ryood/3340VCO/3340VCO性能測定/3340VCO_1kHz.png

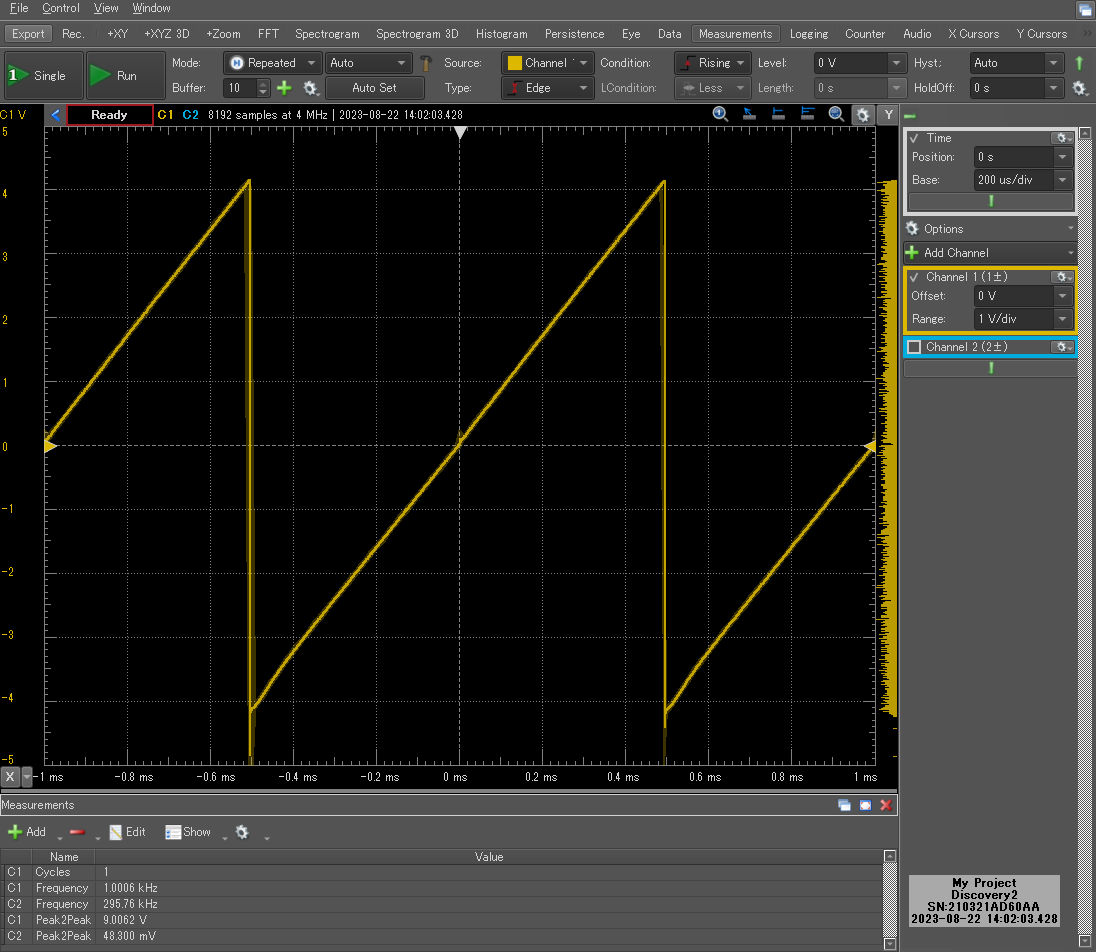
3340VCO性能測定/3340VCO_1kHz.png
