ryood/3340VCO/3340VCO性能測定/3340VCO_CV_Frequency.png

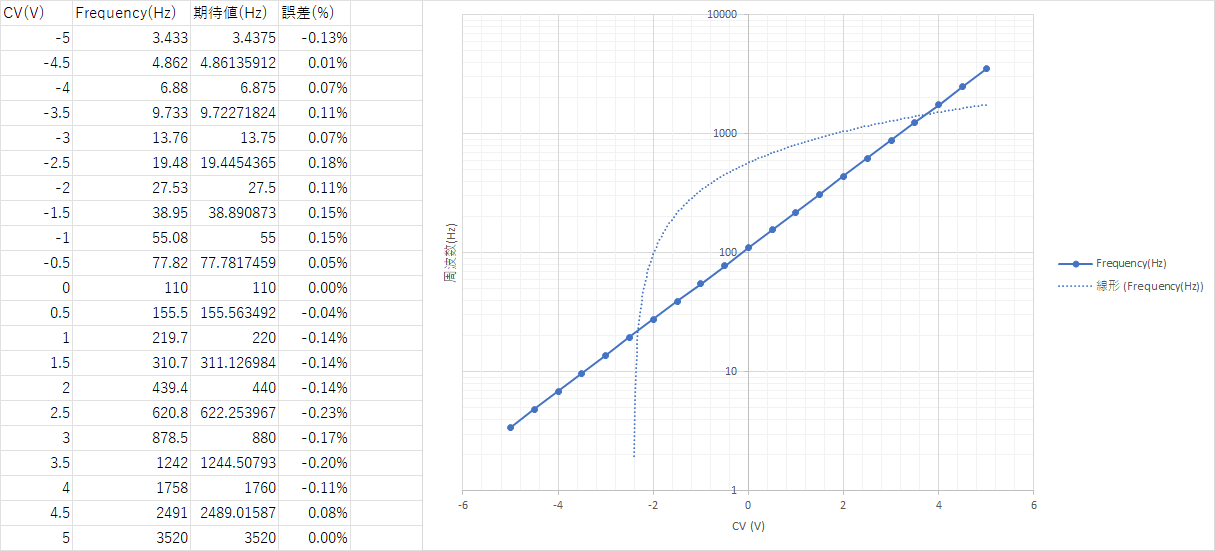
3340VCO性能測定/3340VCO_CV_Frequency.png
