ryood/3340VCO/3340VCO性能測定/3340VCO_SAW_3.43Hz.png

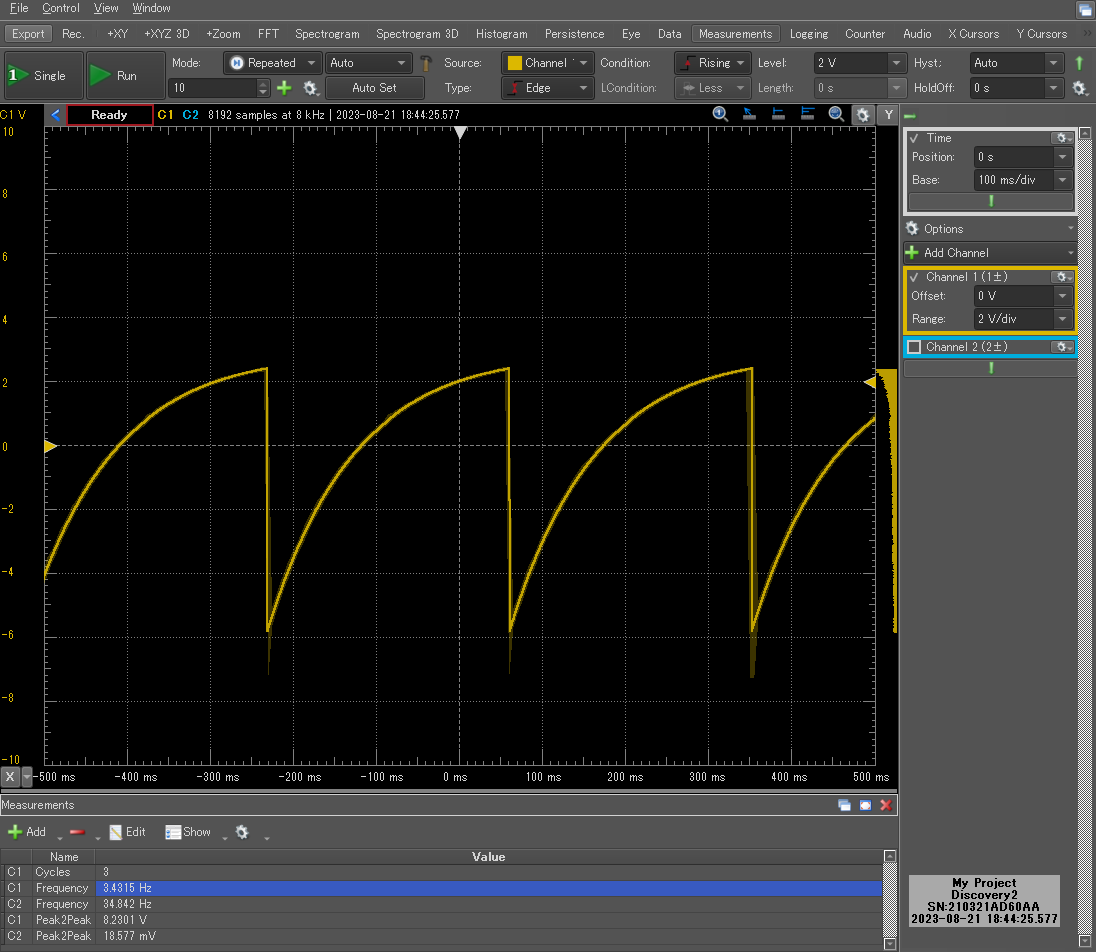
3340VCO性能測定/3340VCO_SAW_3.43Hz.png
