ryood/3340VCO/3340VCO性能測定/3340VCO_Ver.1.1_sch.png

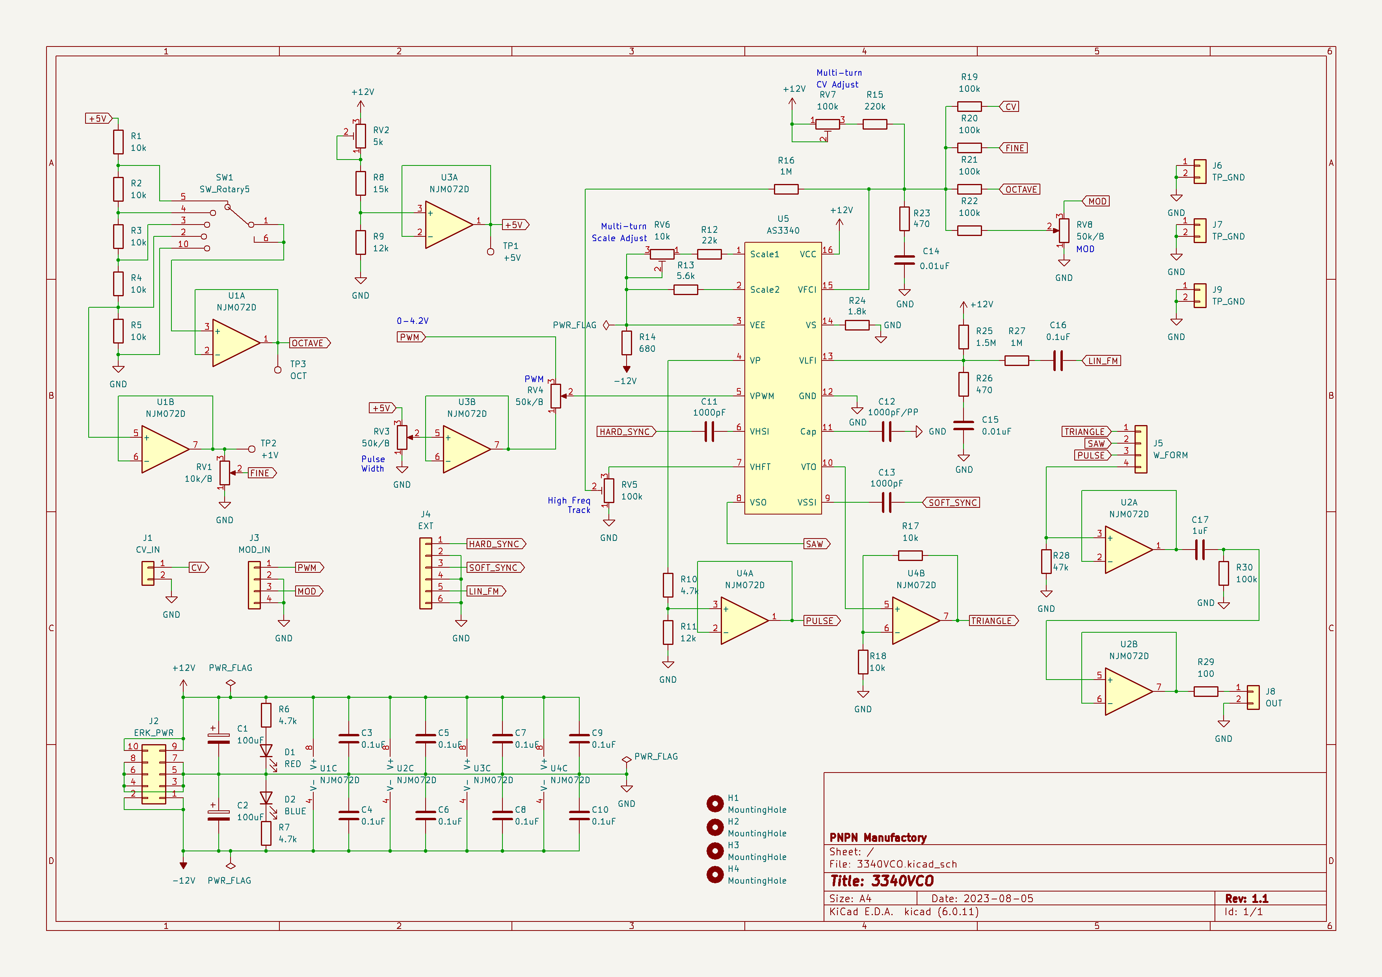
3340VCO性能測定/3340VCO_Ver.1.1_sch.png
