ryood/3340VCO/3340VCO性能測定/AC_CPL_NO.png

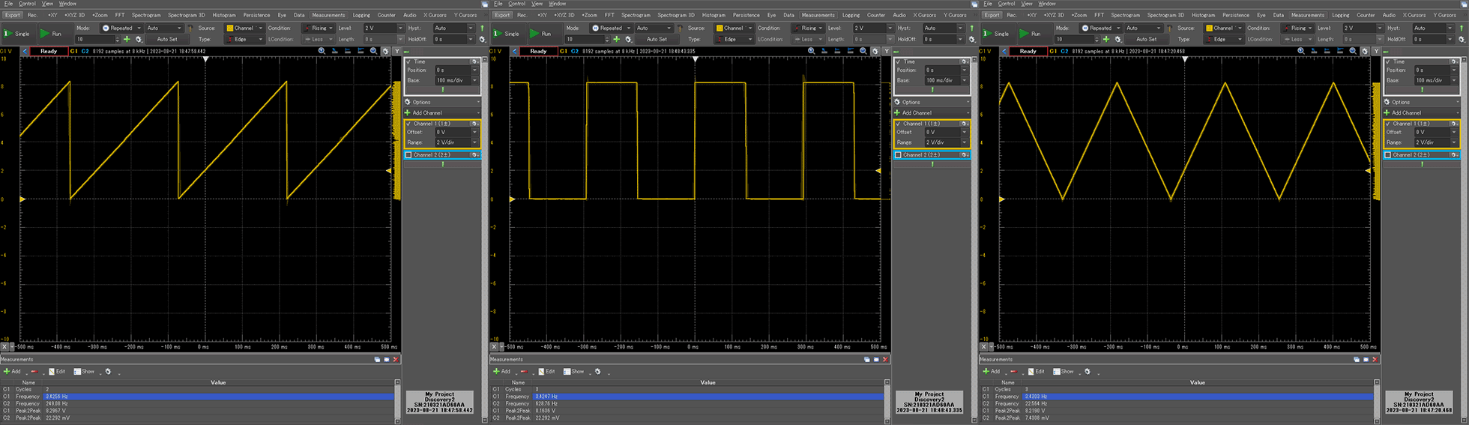
3340VCO性能測定/AC_CPL_NO.png
