ryood/3340VCO/3340VCO性能測定/adder_sim.png

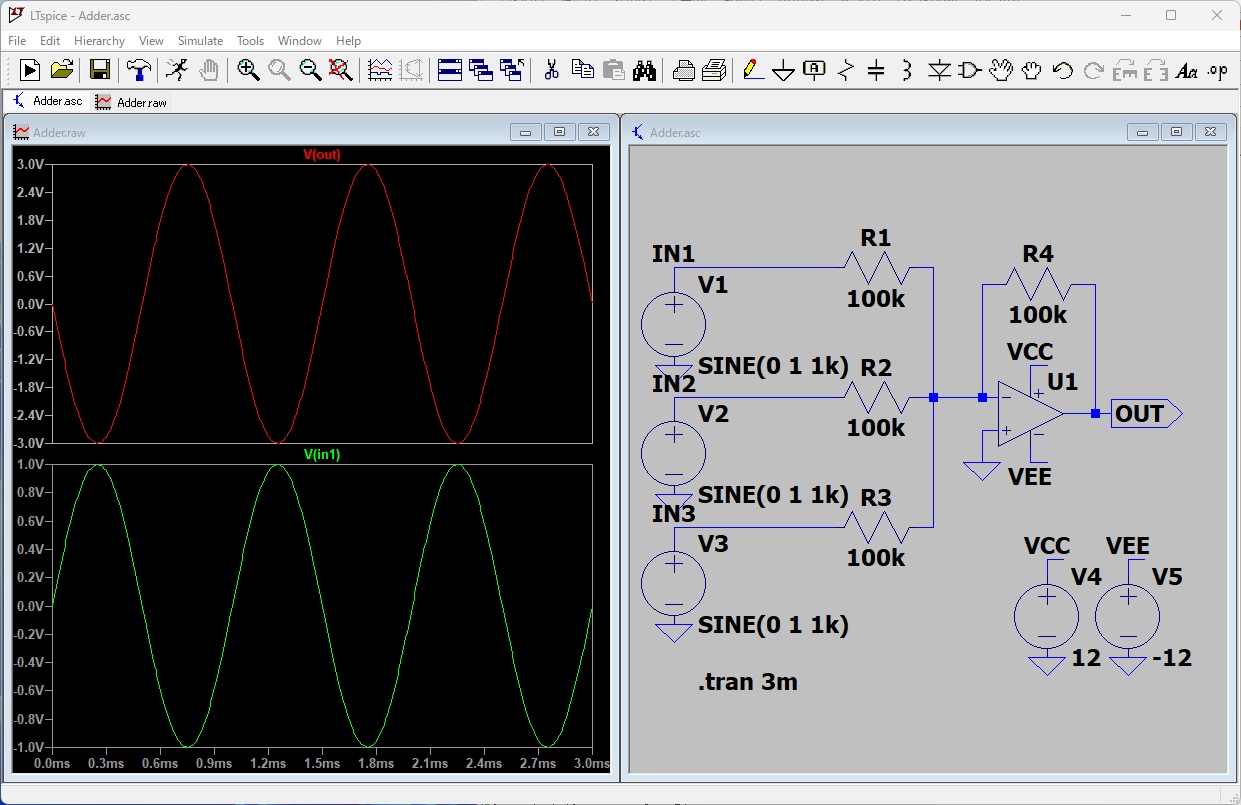
3340VCO性能測定/adder_sim.png
