ryood/3340VCO/3340VCO性能測定/AS3340.png

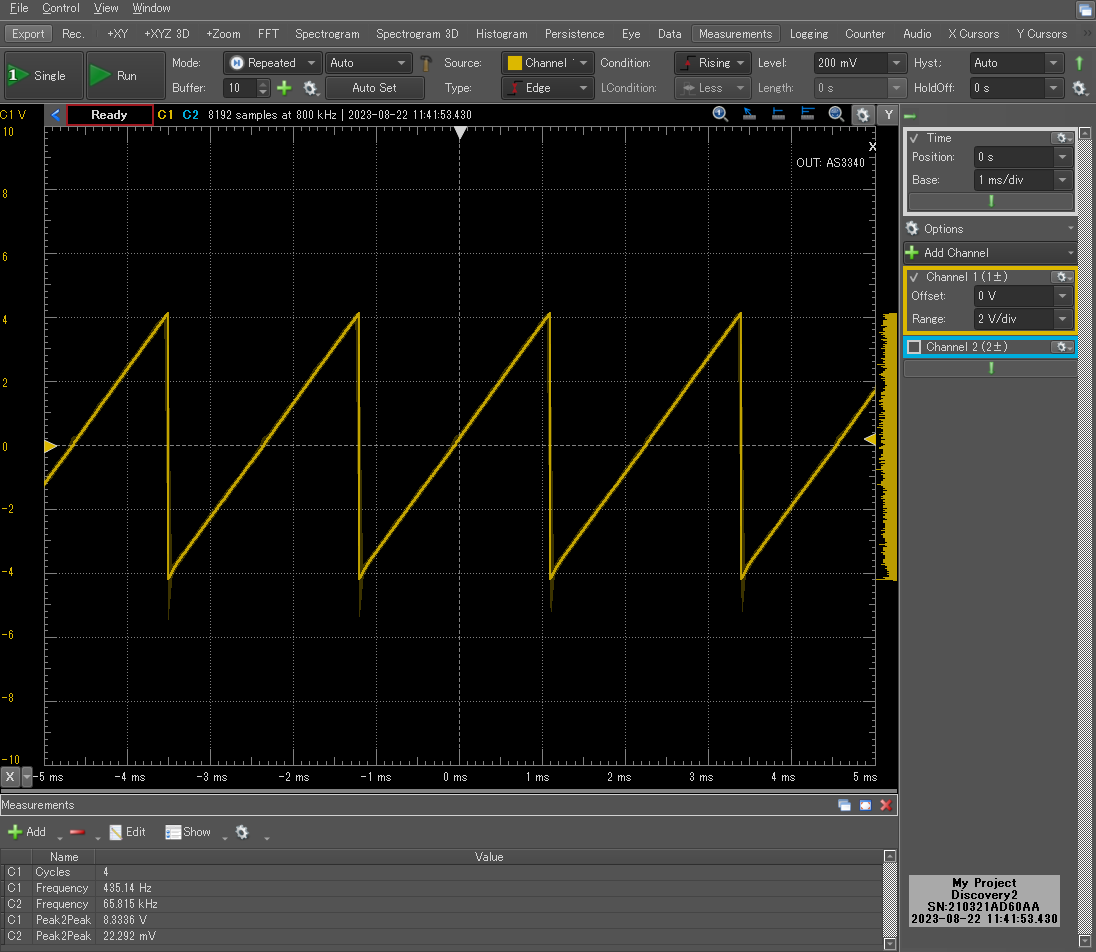
3340VCO性能測定/AS3340.png
