ryood/3340VCO/3340VCO性能測定/HardSync.png

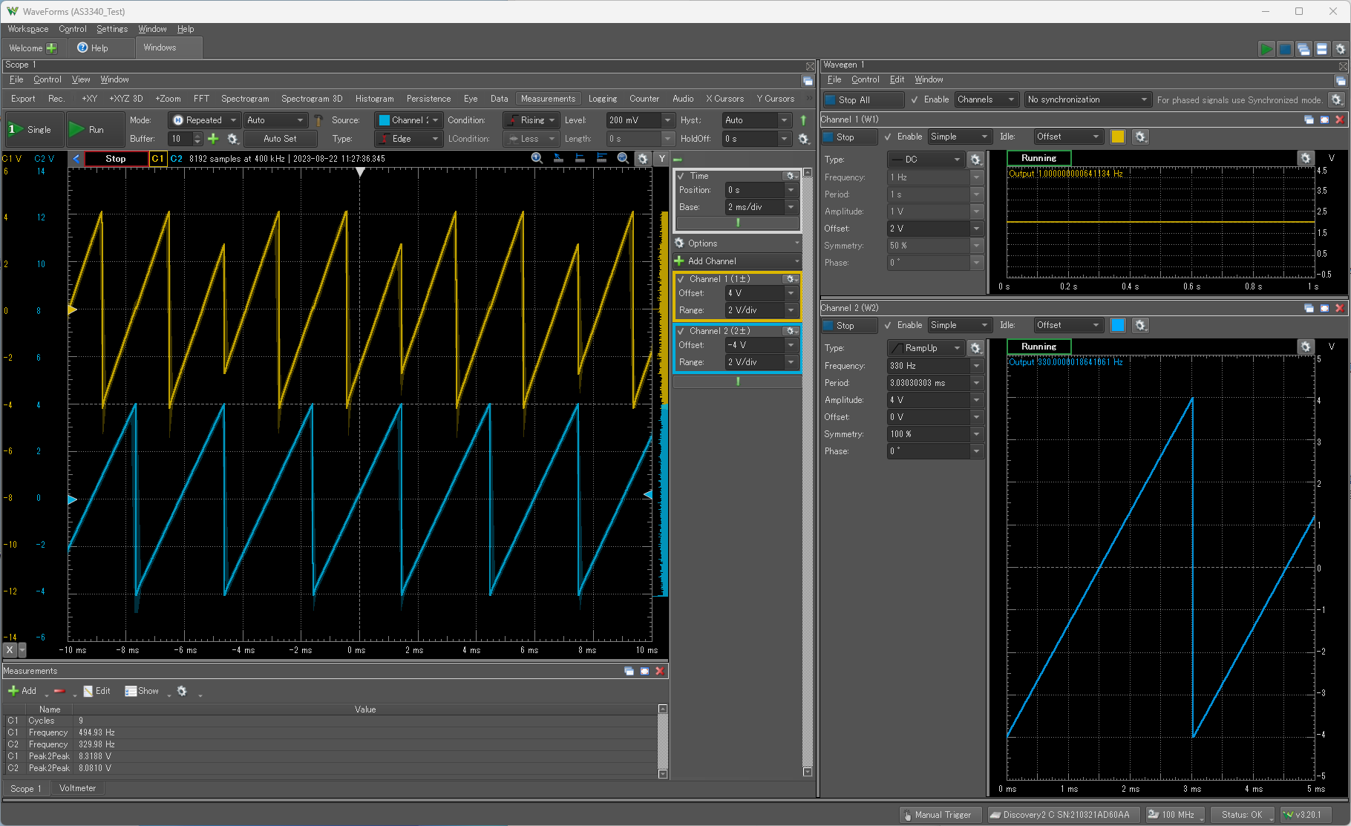
3340VCO性能測定/HardSync.png
