ryood/3340VCO/3340VCO性能測定/LinFM.png

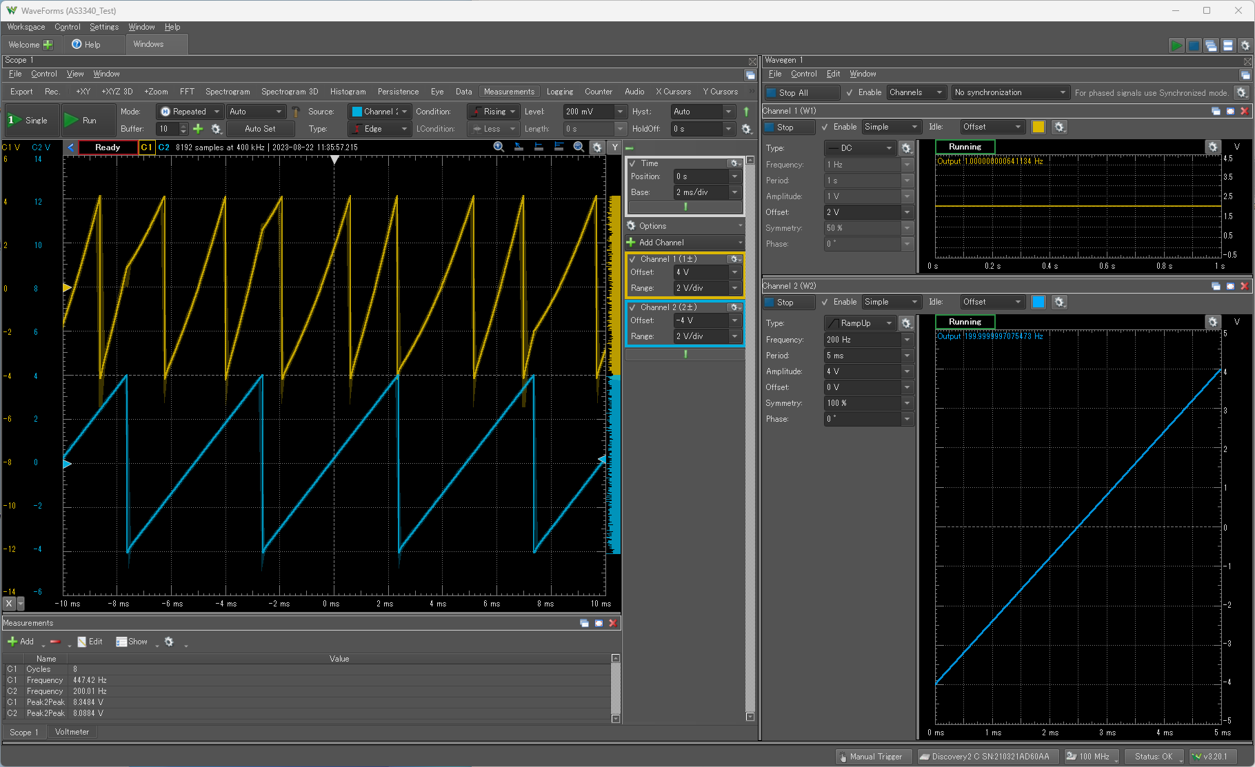
3340VCO性能測定/LinFM.png
