ryood/3340VCO/3340VCO性能測定/MOD_FM.png

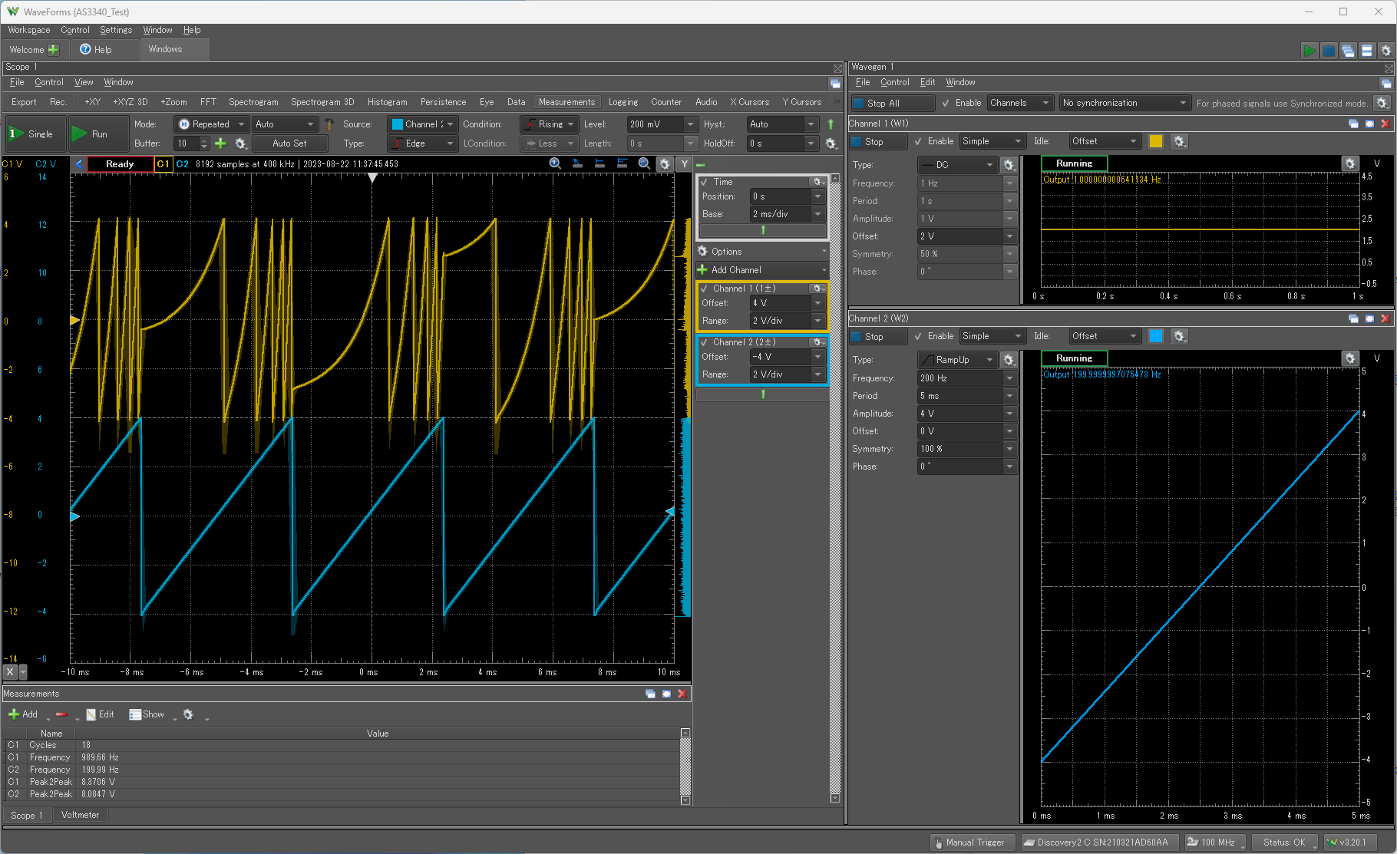
3340VCO性能測定/MOD_FM.png
