ryood/3340VCO/3340VCO性能測定/NO_AC_CPL_3340VCO_SQR_3.43Hz.png

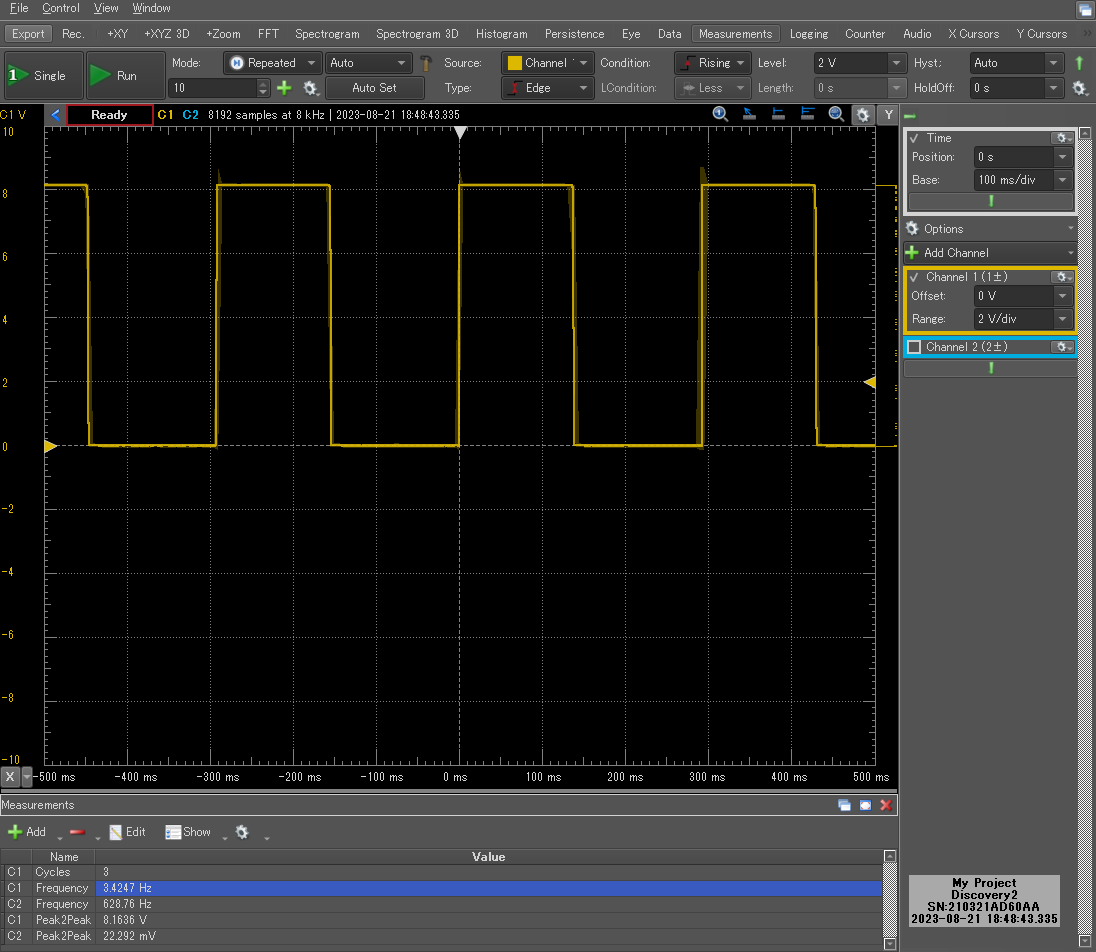
3340VCO性能測定/NO_AC_CPL_3340VCO_SQR_3.43Hz.png
