ryood/3340VCO/3340VCO性能測定/PCM2704_1kHz.png

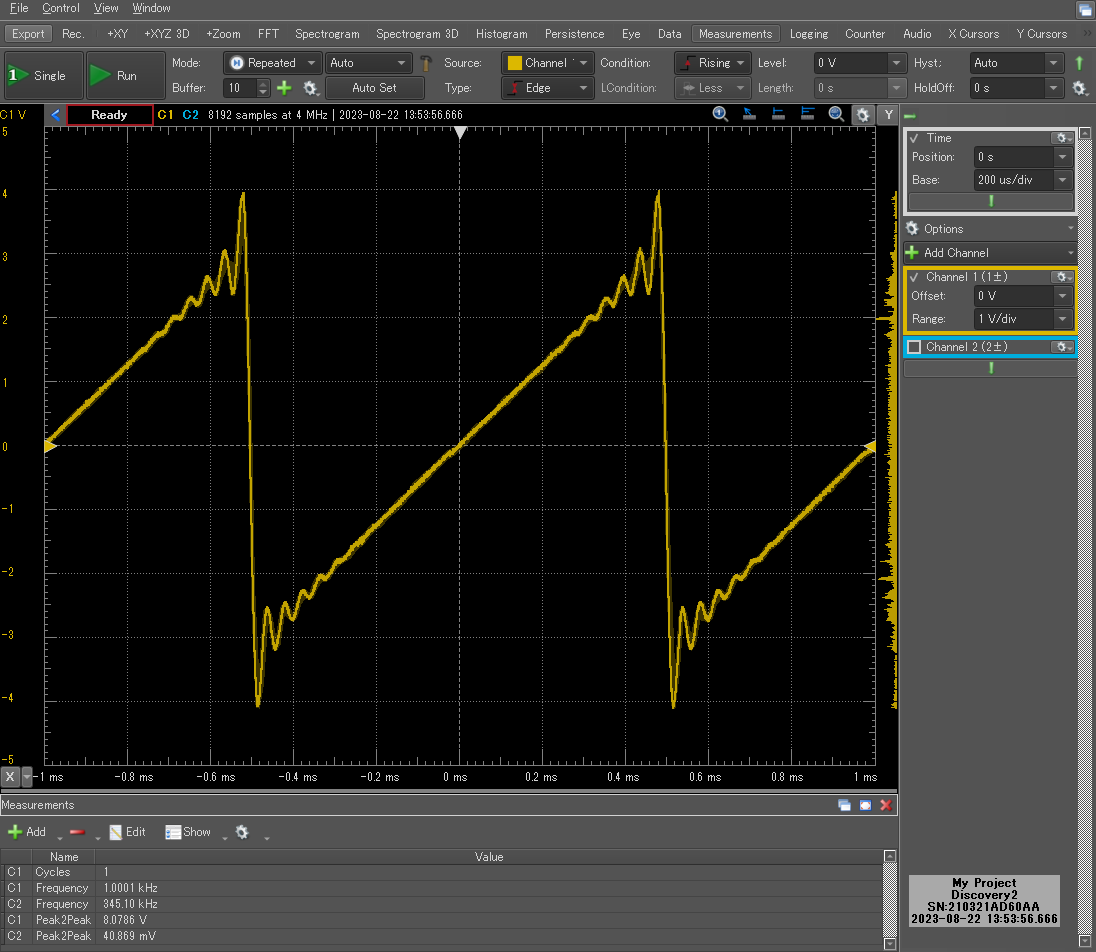
3340VCO性能測定/PCM2704_1kHz.png
