ryood/3340VCO/3340VCO性能測定/SardSync.png

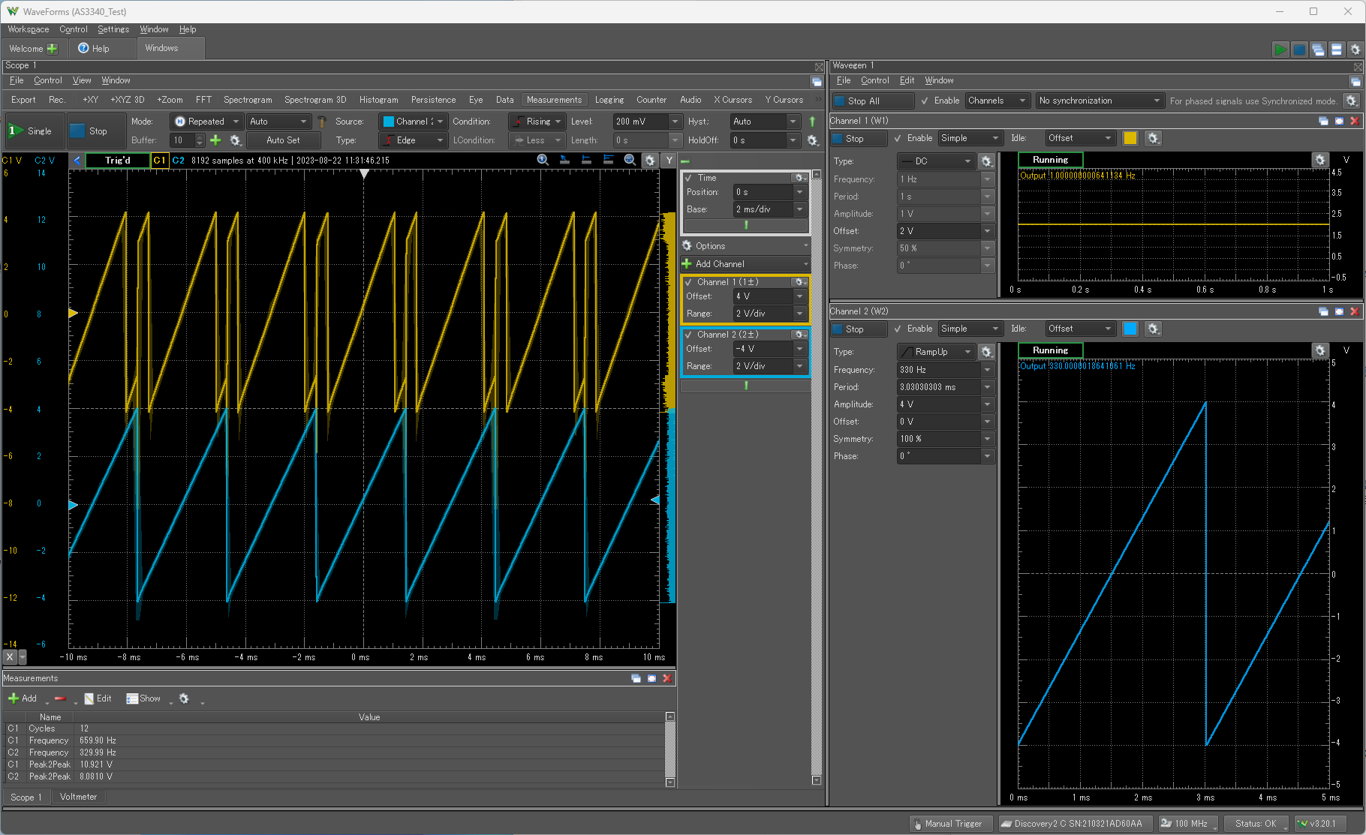
3340VCO性能測定/SardSync.png
