ryood/3340VCO/CAD/3340VCO_panel_tn.png

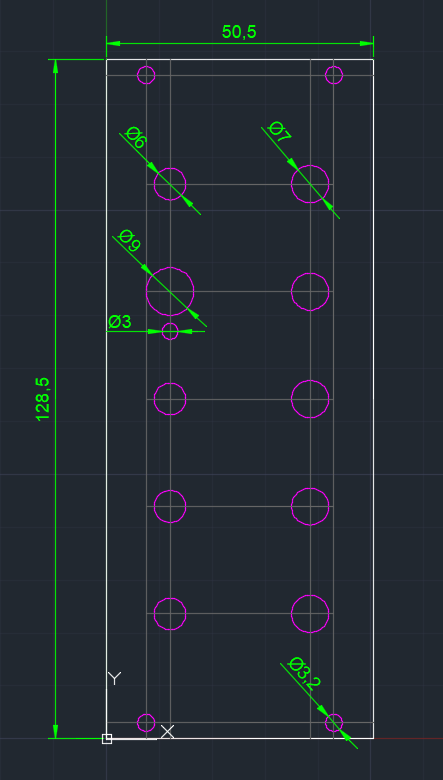
CAD/3340VCO_panel_tn.png
