ryood/3340VCO/etc/Nat_Tsuraichi.jpg

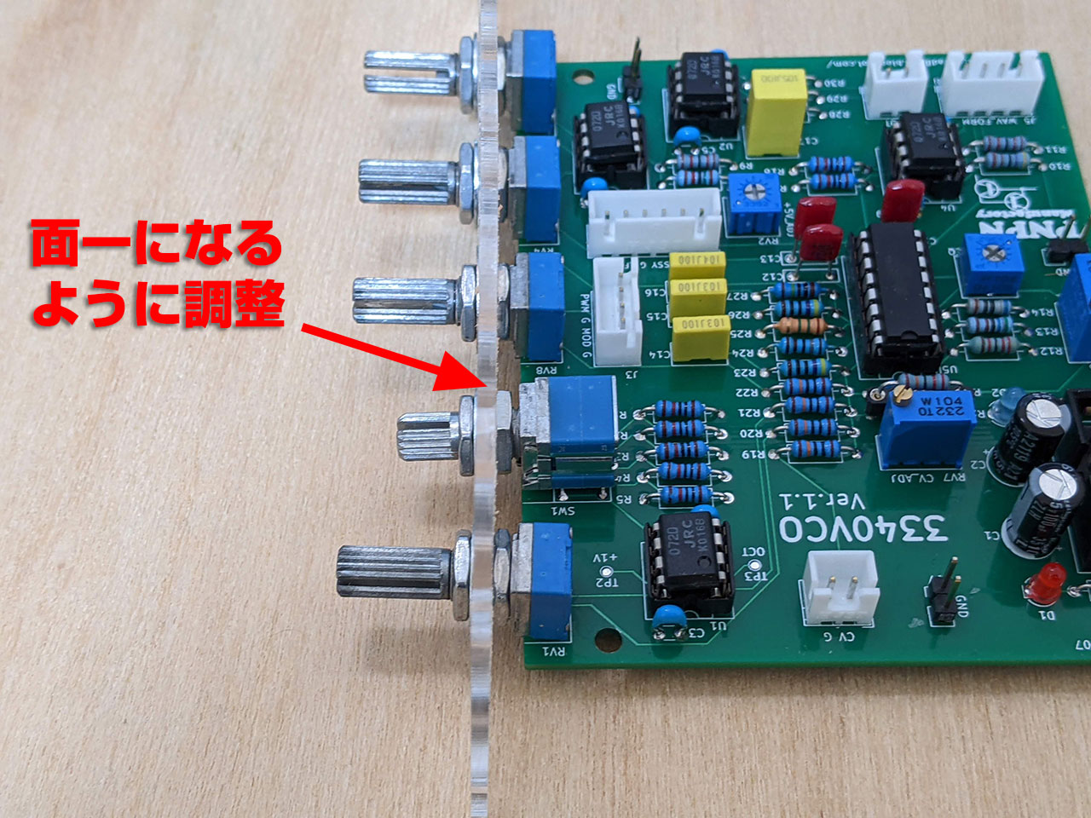
etc/Nat_Tsuraichi.jpg
