ryood/3340VCO/etc/Panel_Nat.jpg

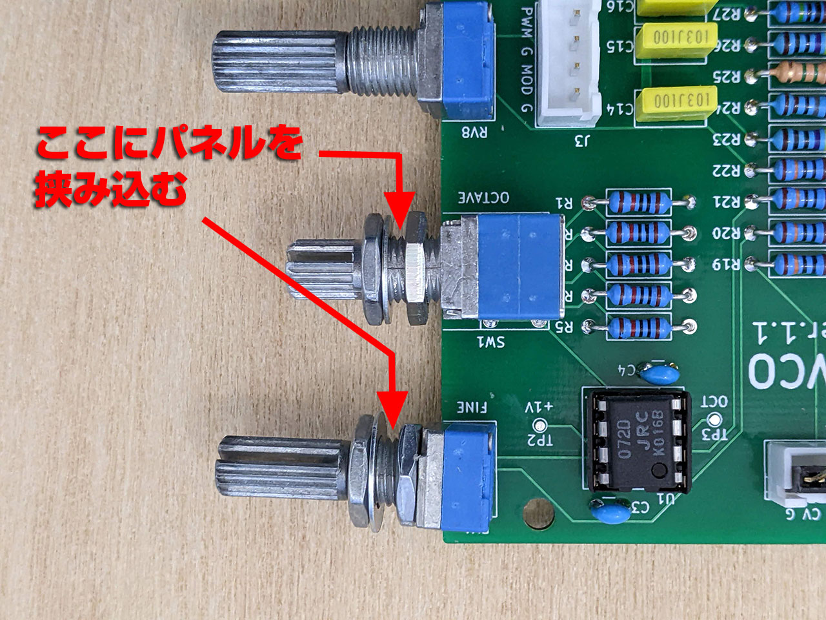
etc/Panel_Nat.jpg
