ryood/3340VCO/etc/PXL_20230715_094157501.jpg

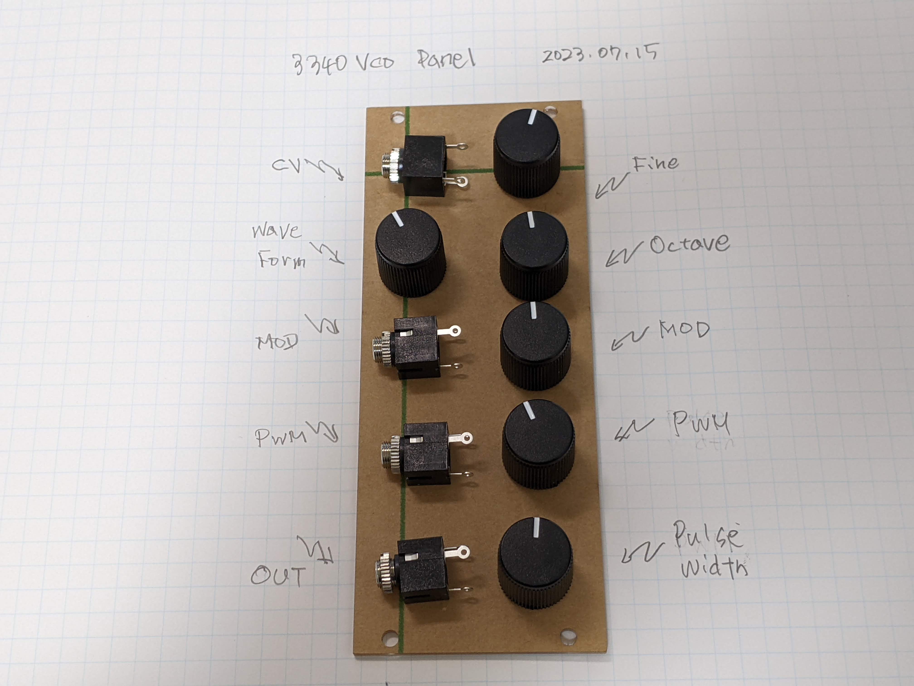
etc/PXL_20230715_094157501.jpg
