ryood/3340VCO/3340VCO性能測定/Adder.asc

R1: res; 100k
R2: res; 100k
R3: res; 100k
R4: res; 100k
U1: UniversalOpAmp2
V1: voltage; SINE(0 1 1k)
V2: voltage; SINE(0 1 1k)
V3: voltage; SINE(0 1 1k)
V4: voltage; 12
V5: voltage; -12
Named nets: VCC, VEE, 0, OUT, IN1, IN2, IN3
.tran 3m
